Totof34/ZRLC_USB/images/PCM2904_3D.png

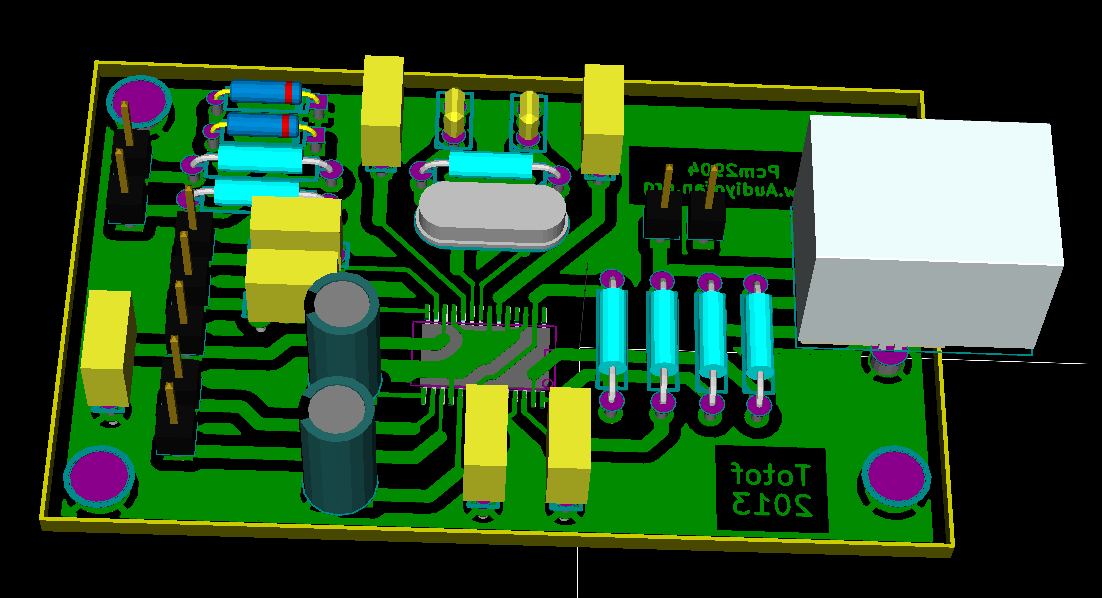
images/PCM2904_3D.png
