Totof34/ZRLC_USB/images/PCM2904_PCB.png

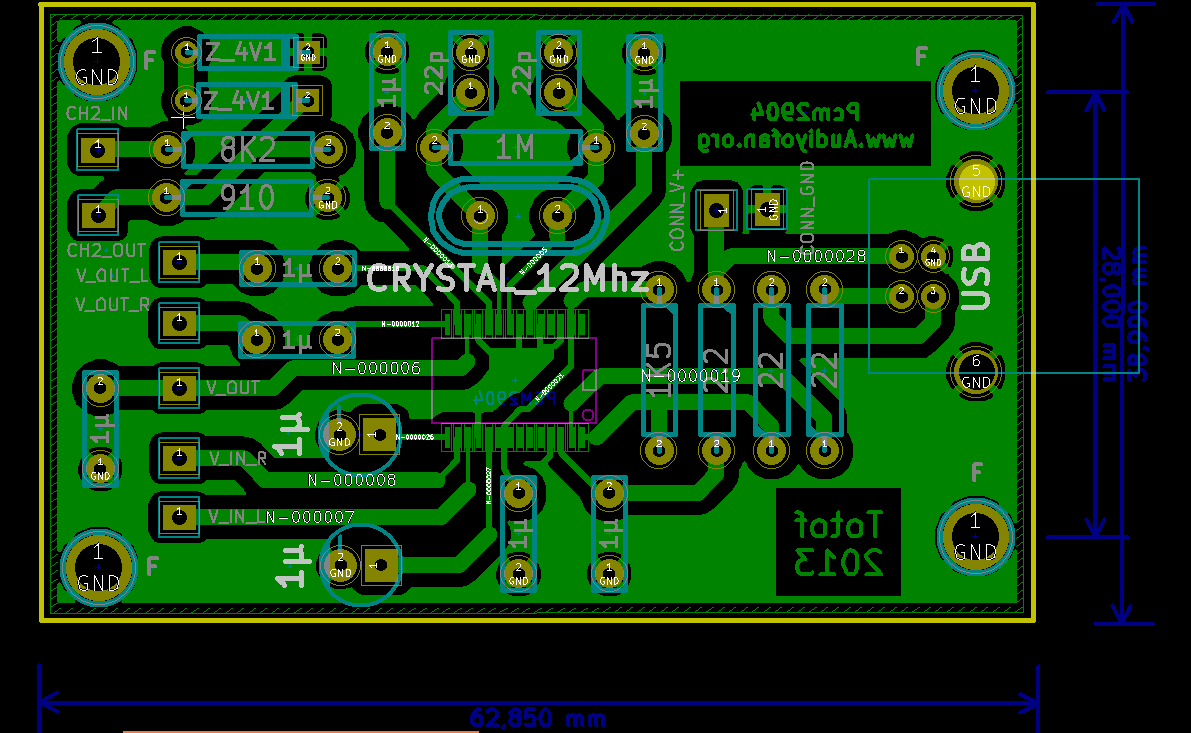
images/PCM2904_PCB.png
