Totof34/ZRLC_USB/schematics/g308_t.jpg

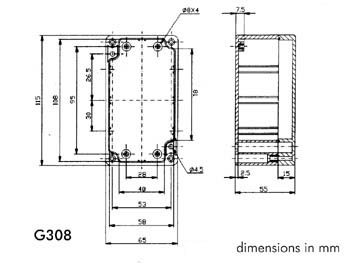
schematics/g308_t.jpg
