Totof34/ZRLC_USB/schematics/m300_t1.jpg

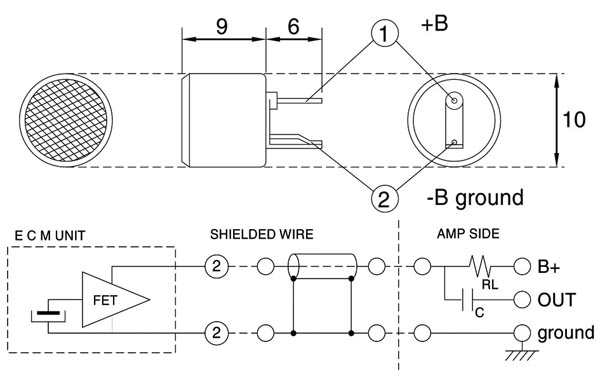
schematics/m300_t1.jpg
